physiii/liger/code/binary_switch/main/binary_switch.c

#include <stdio.h>
#include <string.h>
#include <stdlib.h>
#include "freertos/FreeRTOS.h"
#include "freertos/task.h"
#include "freertos/queue.h"
#include "driver/gpio.h"

#include "xtensa/corebits.h"
#include "esp_spi_flash.h"
#include "esp_system.h"
#include "soc/cpu.h"

#define BINARY_SWITCH_IO     4
#define GPIO_INPUT_PIN_SEL  ((1ULL<<BINARY_SWITCH_IO))
#define ESP_INTR_FLAG_DEFAULT 0
#define DEBOUNCE_TIME 100

static xQueueHandle gpio_evt_queue = NULL;
bool binary_switch_event = false;
bool debounce = false;

/*inline void busy_delay_us(float us) {
  uint32_t t0_ccount, t1_ccount;
  t0_ccount = CCOUNT;
  while (true) {
    RSR(CCOUNT, t1_ccount);
    if (t1_ccount - t0_ccount > ((uint32_t)(us / CPU_TICK_US))) {
      break;
    }
  }
}*/

static void IRAM_ATTR gpio_isr_handler(void* arg)
{
    binary_switch_event = true;
    /*uint32_t gpio_num = (uint32_t) arg;
    if (!debounce) {
        xQueueSendFromISR(gpio_evt_queue, &gpio_num, NULL);
    }*/
}

static void binary_switch_task(void* arg)
{
    for(;;) {
        if (binary_switch_event) {
          binary_switch_event = false;
          int level = gpio_get_level(BINARY_SWITCH_IO);
          printf("BINARY_SWITCH[%d] intr, val: %d\n", BINARY_SWITCH_IO, level);
          debounce = true;
          vTaskDelay(DEBOUNCE_TIME / portTICK_RATE_MS);
          debounce = false;
        }
        vTaskDelay(100 / portTICK_RATE_MS);
    }
}

void app_main()
{
    gpio_config_t io_conf;
    io_conf.intr_type = GPIO_PIN_INTR_POSEDGE;
    io_conf.pin_bit_mask = GPIO_INPUT_PIN_SEL;
    io_conf.mode = GPIO_MODE_INPUT;
    io_conf.pull_up_en = 1;
    gpio_config(&io_conf);

    //change gpio intrrupt type for one pin
    gpio_set_intr_type(BINARY_SWITCH_IO, GPIO_INTR_ANYEDGE);
    //create a queue to handle gpio event from isr
    gpio_evt_queue = xQueueCreate(10, sizeof(uint32_t));
    xTaskCreate(binary_switch_task, "binary_switch_task", 2048, NULL, 10, NULL);

    //install gpio isr service
    gpio_install_isr_service(ESP_INTR_FLAG_DEFAULT);
    gpio_isr_handler_add(BINARY_SWITCH_IO, gpio_isr_handler, (void*) BINARY_SWITCH_IO);
}
